merlinmarrs/iCE40HX-verilog-video-patterns/IMG_3939.jpg

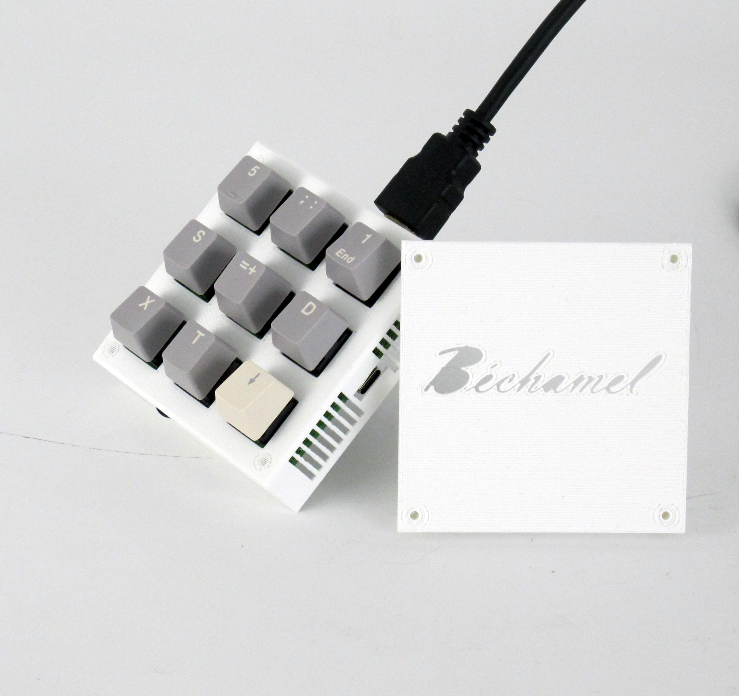
IMG_3939.jpg
