merlinmarrs/iCE40HX-verilog-video-patterns/verilog/vga_sync_test_5.v

`default_nettype none

module vga_sync_test(

input wire clk_in,
input wire reset,

//VGA OUT
output reg [3:0] r_out,
output reg [3:0] b_out,
output reg [3:0] g_out,

output wire h_sync,
output wire v_sync

);


wire half_sec;

wire [12:0] random_number_0;
wire [12:0] random_number_1;
wire [12:0] random_number_2;
wire [12:0] random_number_3;
wire [12:0] random_number_4;
wire [12:0] random_number_5;
wire [12:0] random_number_6;
wire [12:0] random_number_7;
wire [12:0] random_number_8;
wire [12:0] random_number_9;
wire [7:0] sine_wave;

wire display_en;
wire [11:0] h_count;
wire [11:0] v_count;

localparam h_pixel_max = 1280;
localparam v_pixel_max = 960;
localparam h_pixel_half = 640;
localparam v_pixel_half = 480;

reg [1:0] count2; //to keep track of the shifts

wire [11:0] bit_or;
assign bit_or = h_count[11:0]|v_count[11:0];

wire [11:0] bit_xor;
assign bit_xor = h_count[11:0]^v_count[11:0];

wire [11:0] bit_and;
assign bit_and = h_count[11:0]&v_count[11:0];

wire [11:0] bit_nand;
assign bit_nand = h_count[11:0]& ~v_count[11:0];

wire [11:0] bit_xnor;
assign bit_xnor = h_count[11:0]^ ~v_count[11:0];

reg [11:0] out_bit ;


//VGA COLOR OUT

always @(posedge clk_in) begin

      						  case(count2)
         						 2'b00: out_bit = bit_or;  
         						 2'b01: out_bit = bit_xor;
          						 2'b10: out_bit = bit_and;
          					        2'b11: out_bit = bit_nand;			

                                              default: out_bit = bit_xnor;
                                              endcase
count2  <= count2 + 1;


if (display_en) begin


if (h_count <  random_number_0[7:0]) begin

r_out <= random_number_2[3:0];
g_out <= random_number_3[3:0];
b_out <= random_number_4[3:0];

end

else if (h_count <  random_number_0[7:0] + random_number_2[8:0]) begin



r_out <= random_number_2[3:0];
g_out <= random_number_3[3:0];
b_out <= random_number_4[3:0];

end

else if (h_count <  random_number_0[8:0] + random_number_2[8:0] + random_number_8[8:0]) begin

r_out <= random_number_5[3:0];
g_out <= random_number_5[3:0];
b_out <= random_number_8[3:0];

end

else if (h_count <  random_number_0[7:0] + random_number_2[12:4] + random_number_8[11:5] + random_number_3[8:1] ) begin

r_out <= random_number_0[3:0];
g_out <= random_number_9[3:0];
b_out <= random_number_0[3:0];

end

else if (h_count <  random_number_0[8:2] + random_number_2[8:2] + random_number_8[9:3] + random_number_3[7:1] + random_number_4[9:2] ) begin

r_out <= random_number_8[3:0];
g_out <= random_number_1[3:0];
b_out <= random_number_8[3:0];

end

else if (h_count <  random_number_0[9:2] + random_number_2[9:1] + random_number_8[8:0] + random_number_3[11:4] + random_number_4[10:6] + random_number_5[8:0]) begin

r_out <= random_number_3[3:0];
g_out <= random_number_4[3:0];
b_out <= random_number_5[3:0];

end

else if (h_count < random_number_0[12:9] + random_number_2[12:6] + random_number_8[10:5] + random_number_3[9:2] + random_number_4[7:0] + random_number_5[9:0]+ random_number_6[12:0]) begin

r_out <= random_number_6[3:0];
g_out <= random_number_7[3:0];
b_out <= random_number_6[3:0];

end

else if (h_count <  random_number_0[6:0] + random_number_2[9:2] + random_number_8[9:2] + random_number_3[10:5] + random_number_4[9:2] + random_number_5[8:1]+ random_number_6[5:1]+ random_number_7[6:0]) begin

r_out <= random_number_9[3:0];
g_out <= random_number_9[3:0];
b_out <= random_number_2[3:0];

end

end 

else begin

r_out <= 4'b0000;
g_out <= 4'b0000;
b_out <= 4'b0000;

end

end 

vga_sync vga_s(
.clk_in(clk_in),
.reset(reset),
.h_sync(h_sync),
.v_sync(v_sync),
.h_count(h_count),
.v_count(v_count),
.display_en(display_en) // '1' => pixel region
);

LFSR random_s(
    .clock(clk_in),
    .reset(reset),
    .half_sec_pulse(half_sec),
    .rnd_0(random_number_0),
    .rnd_1(random_number_1),
    .rnd_2(random_number_2),
    .rnd_3(random_number_3),
    .rnd_4(random_number_4),
    .rnd_5(random_number_5),
    .rnd_6(random_number_6),
    .rnd_7(random_number_7),
    .rnd_8(random_number_8),
    .rnd_9(random_number_9)
    );

sine_wave_gen sine_wave_s(
    .clk(clk_in),
    .data_out(sine_wave)
    );

tempo tempo_s(
    .clk(clk_in),
    .half_sec_pulse(half_sec)
    );

endmodule
